labamichnetvoll/HM_MechInt_Alarmanlage/Schaltplan/01_HM_Alarmanlage/01_HM_Alarmanlage.kicad_sch

## KiCad design Schaltplan/01_HM_Alarmanlage/01_HM_Alarmanlage.kicad_sch (2026-01-06, an earlier design)

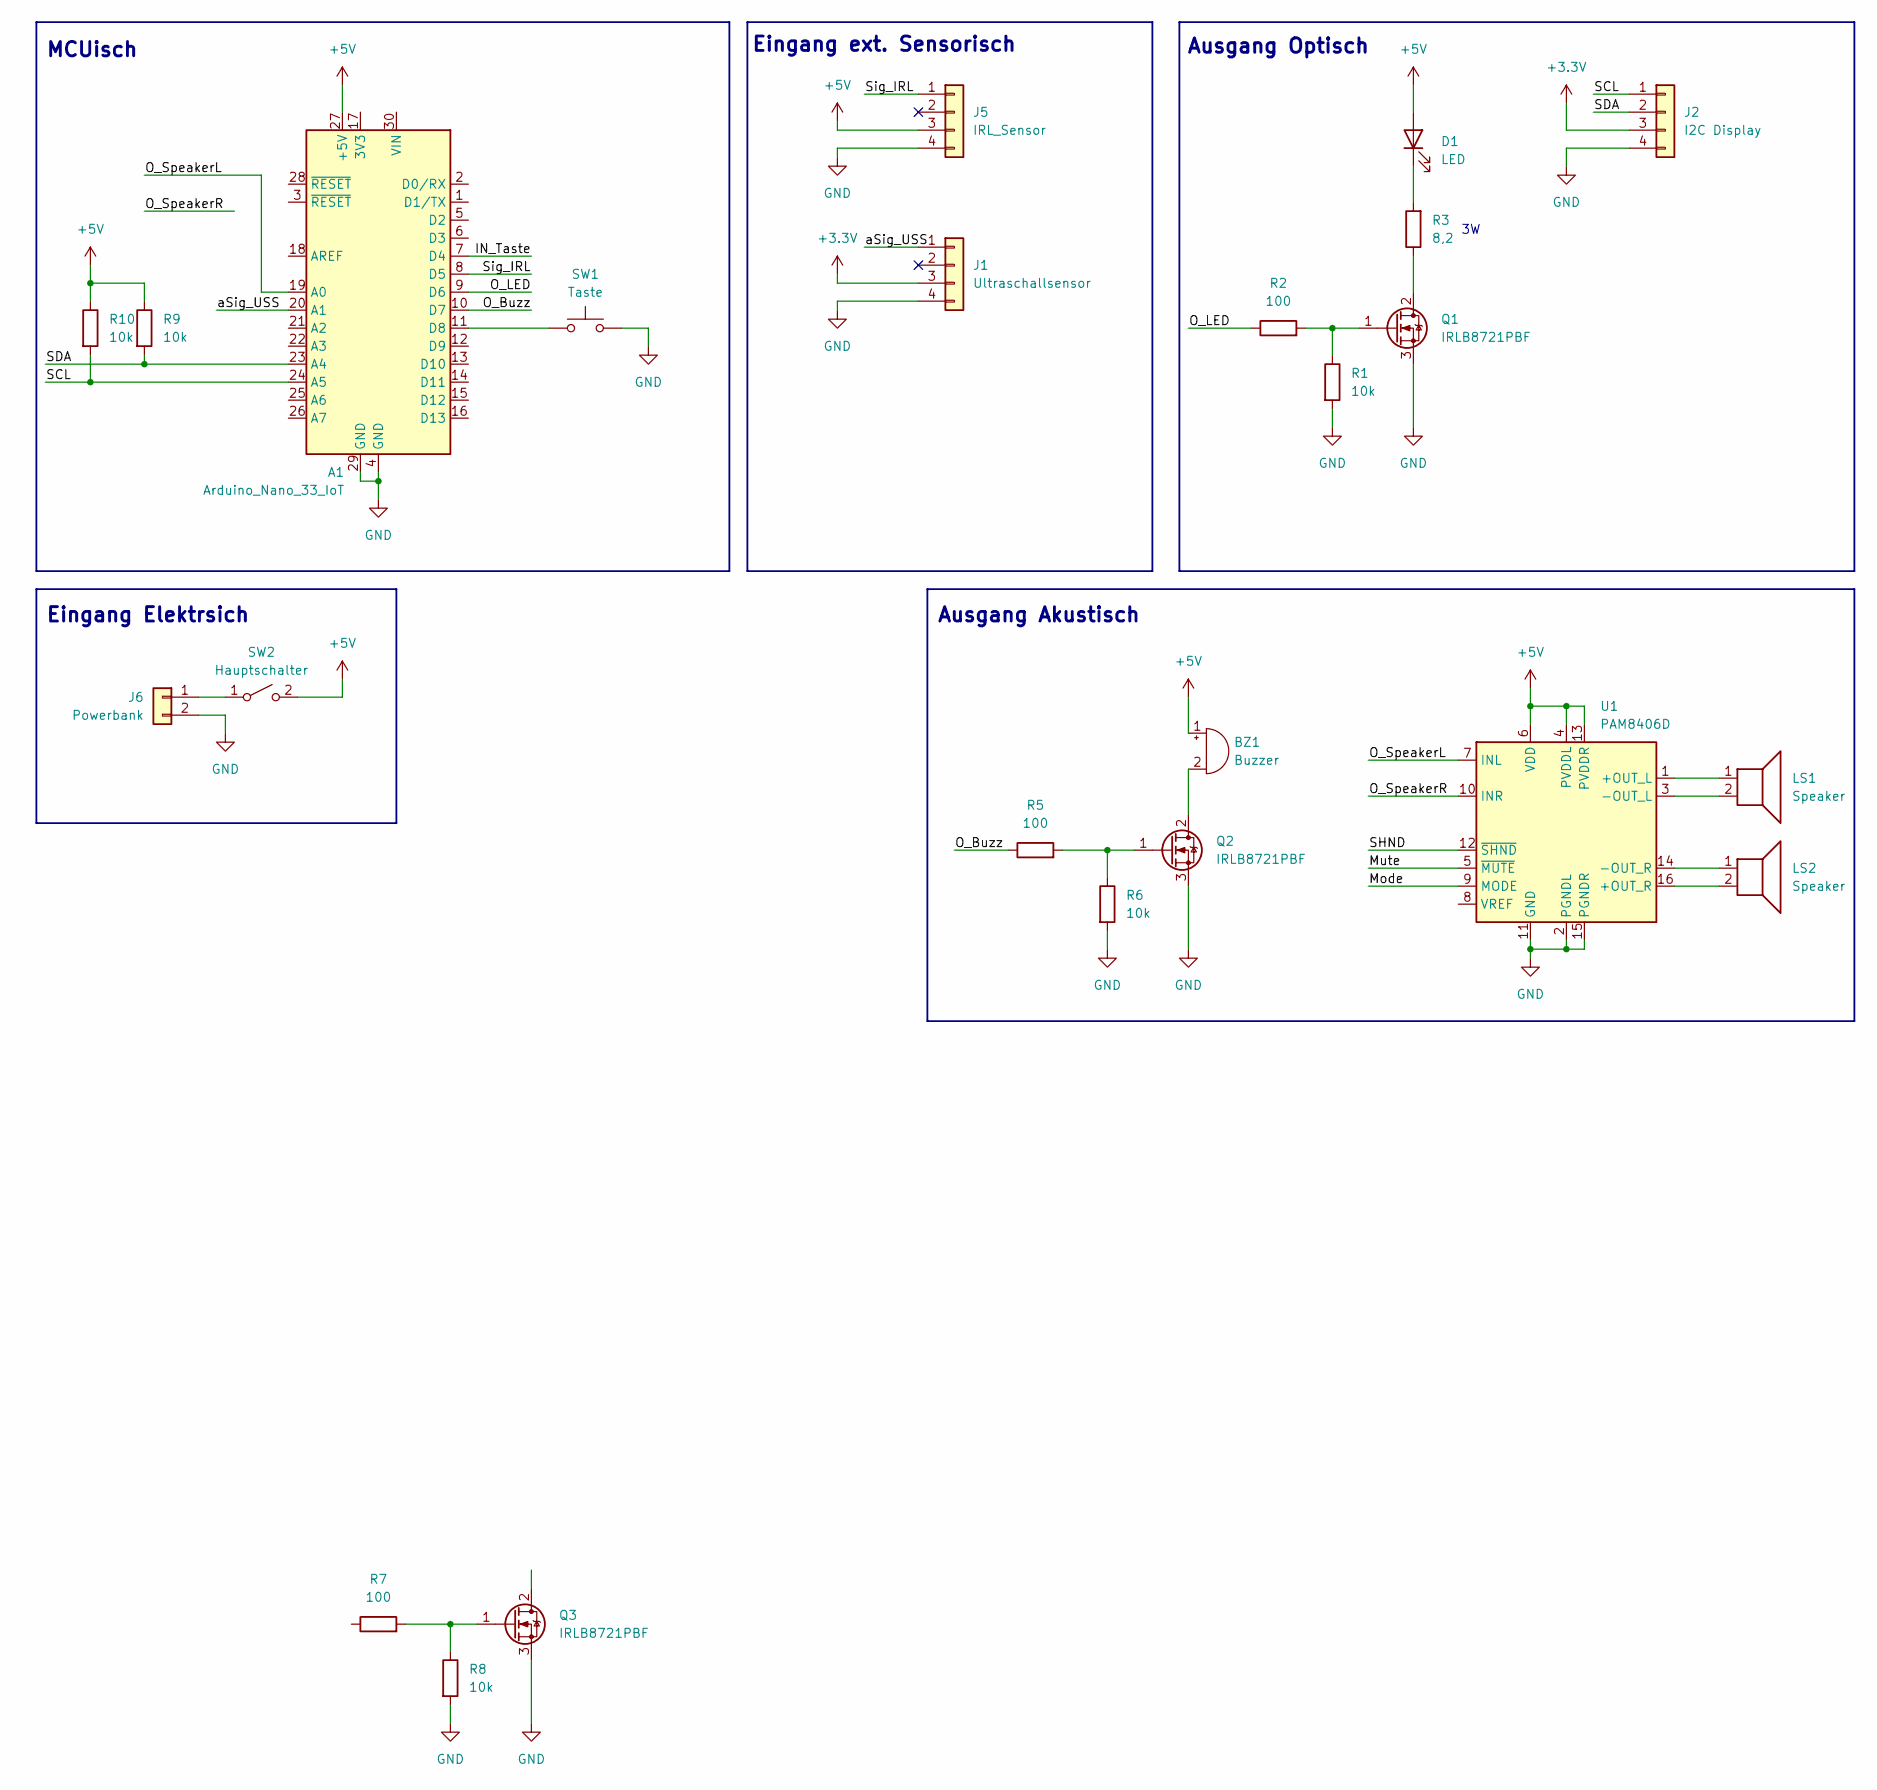
[picture p2: schematic 01_HM_Alarmanlage.kicad_sch]

Parts:
A1: Arduino_Nano_33_IoT; Arduino_Nano
BZ1: Buzzer
D1: LED
J1: Ultraschallsensor
J2: I2C Display
J5: IRL_Sensor
J6: Powerbank
LS1, LS2: Speaker
Q1, Q2, Q3: IRLB8721PBF; TO-220-3_Vertical
R1, R6, R8, R9, R10: 10k
R2, R5, R7: 100
R3: 8,2
SW1: Taste
SW2: Hauptschalter
U1: PAM8406D; SOIC-16_3.9x9.9mm_P1.27mm

Connections:
+3.3V: J1.3, J2.3
+5V: A1.27 (+5V), BZ1.1 (+), D1.2 (A), J5.3, R9.1, R10.1, SW2.2 (B), U1.4 (PVDDL), U1.6 (VDD), U1.13 (PVDDR)
GND: A1.4 (GND), A1.29 (GND), J1.4, J2.4, J5.4, J6.2, Q1.3 (S), Q2.3 (S), Q3.3 (S), R1.2, R6.2, R8.2, SW1.2, U1.2 (PGNDL), U1.11 (GND), U1.15 (PGNDR)
IN_Taste: A1.7 (D4)
Mode: U1.9 (MODE)
Mute: U1.5 (~MUTE)
unnamed: A1.11 (D8), SW1.1
unnamed: BZ1.2 (-), Q2.2 (D)
unnamed: D1.1 (K), R3.2
unnamed: J6.1, SW2.1 (A)
unnamed: LS1.1, U1.1 (+OUT_L)
unnamed: LS1.2, U1.3 (-OUT_L)
unnamed: LS2.1, U1.14 (-OUT_R)
unnamed: LS2.2, U1.16 (+OUT_R)
unnamed: Q1.1 (G), R1.1, R2.2
unnamed: Q1.2 (D), R3.1
unnamed: Q2.1 (G), R5.2, R6.1
unnamed: Q3.1 (G), R7.2, R8.1
O_Buzz: A1.10 (D7), R5.1
O_LED: A1.9 (D6), R2.1
O_SpeakerL: A1.19 (A0), U1.7 (INL)
O_SpeakerR: U1.10 (INR)
SCL: A1.24 (A5), J2.1, R10.2
SDA: A1.23 (A4), J2.2, R9.2
SHND: U1.12 (~SHND)
Sig_IRL: A1.8 (D5), J5.1
aSig_USS: A1.20 (A1), J1.1

Notes on the sheet:
Eingang Elektrsich
Ausgang Akustisch
Ausgang Optisch
MCUisch
Eingang ext. Sensorisch
