labamichnetvoll/HM_MechInt_Alarmanlage/Schaltplan/01_HM_Alarmanlage/Lautsprecher.kicad_sch

## KiCad design Schaltplan/01_HM_Alarmanlage/Lautsprecher.kicad_sch (2026-01-06)

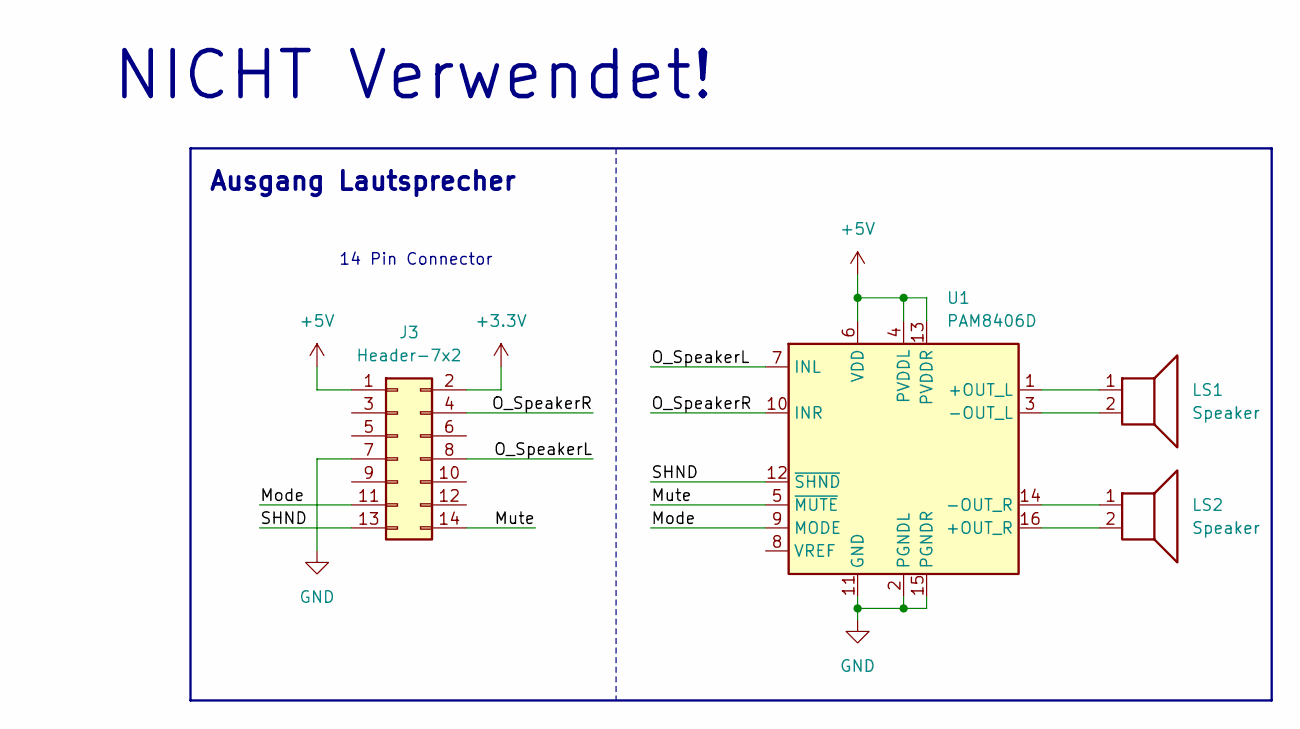
[picture p3: schematic Lautsprecher.kicad_sch]

Parts:
J3: Header-7x2
LS1, LS2: Speaker
U1: PAM8406D; SOIC-16_3.9x9.9mm_P1.27mm

Connections:
+3.3V: J3.2
+5V: J3.1, U1.4 (PVDDL), U1.6 (VDD), U1.13 (PVDDR)
GND: J3.7, U1.2 (PGNDL), U1.11 (GND), U1.15 (PGNDR)
Mode: J3.11, U1.9 (MODE)
Mute: J3.14, U1.5 (~MUTE)
unnamed: LS1.1, U1.1 (+OUT_L)
unnamed: LS1.2, U1.3 (-OUT_L)
unnamed: LS2.1, U1.14 (-OUT_R)
unnamed: LS2.2, U1.16 (+OUT_R)
O_SpeakerL: J3.8, U1.7 (INL)
O_SpeakerR: J3.4, U1.10 (INR)
SHND: J3.13, U1.12 (~SHND)

Notes on the sheet:
14 Pin Connector
NICHT Verwendet!
Ausgang Lautsprecher
